RBEGamer/DBClock/documentation/images/2023-02-08 12.05.27.jpg

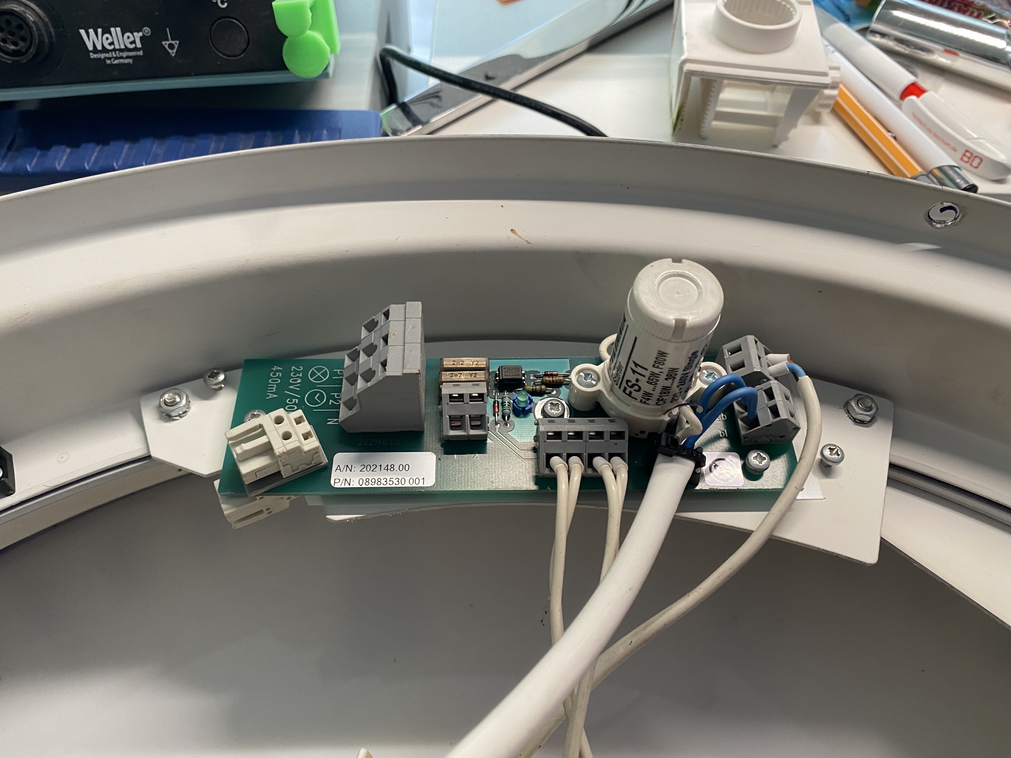
documentation/images/2023-02-08 12.05.27.jpg
