RBEGamer/DBClock/documentation/images/2023-02-08 12.11.48.jpg

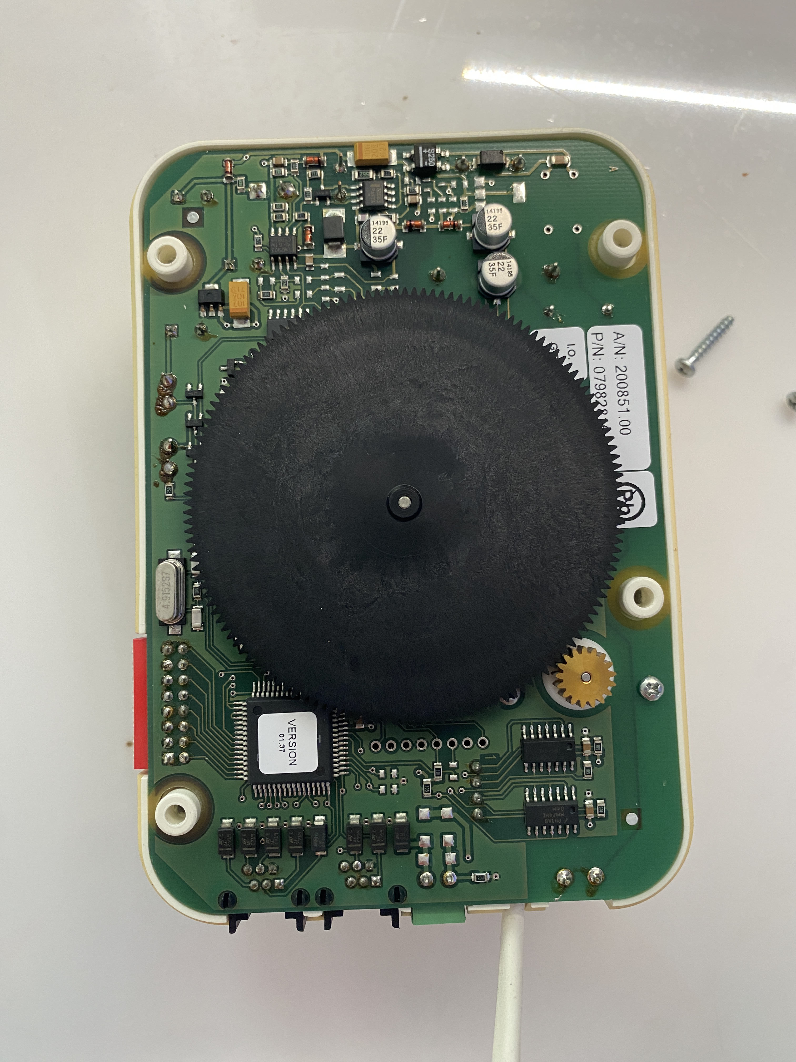
documentation/images/2023-02-08 12.11.48.jpg
