RBEGamer/DBClock/documentation/images/2023-02-12 22.21.10.jpg

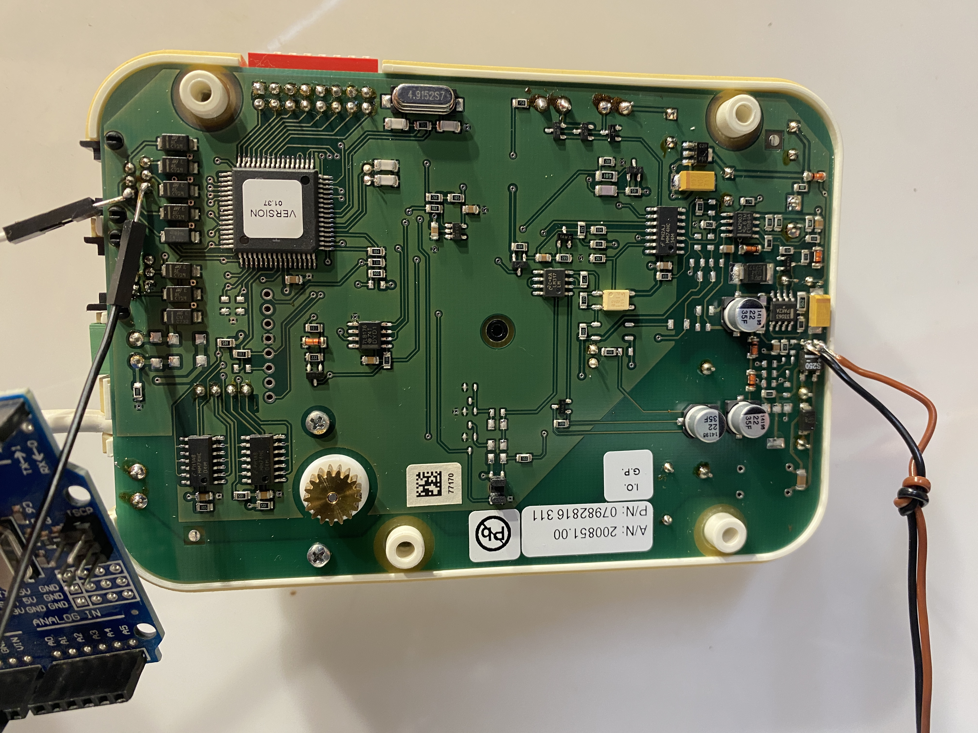
documentation/images/2023-02-12 22.21.10.jpg
