RBEGamer/DBClock/documentation/images/2023-02-13 15.05.28.jpg

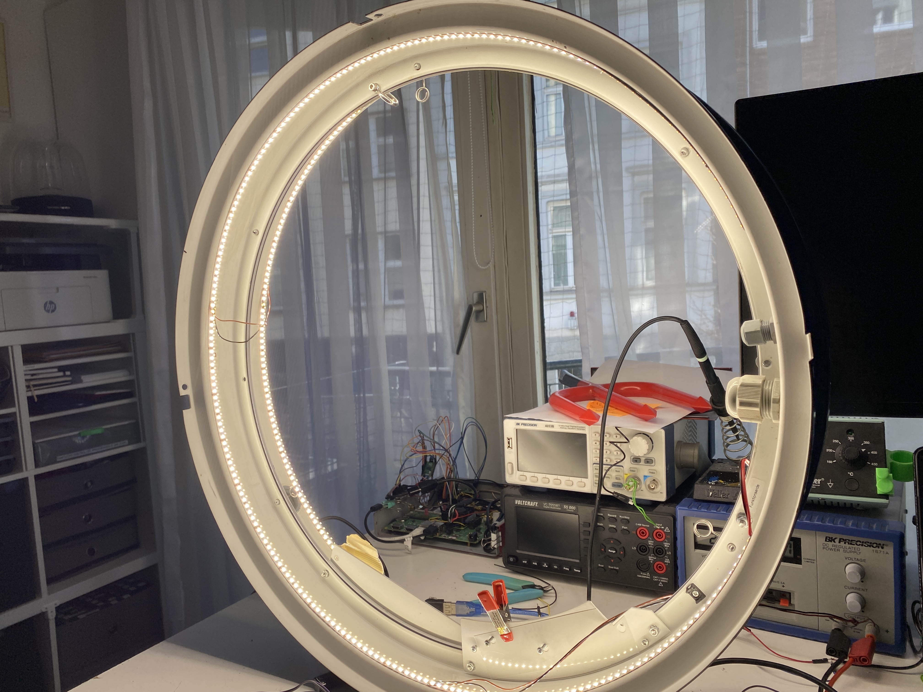
documentation/images/2023-02-13 15.05.28.jpg
