RBEGamer/DBClock/documentation/images/2023-02-14 12.46.16.jpg

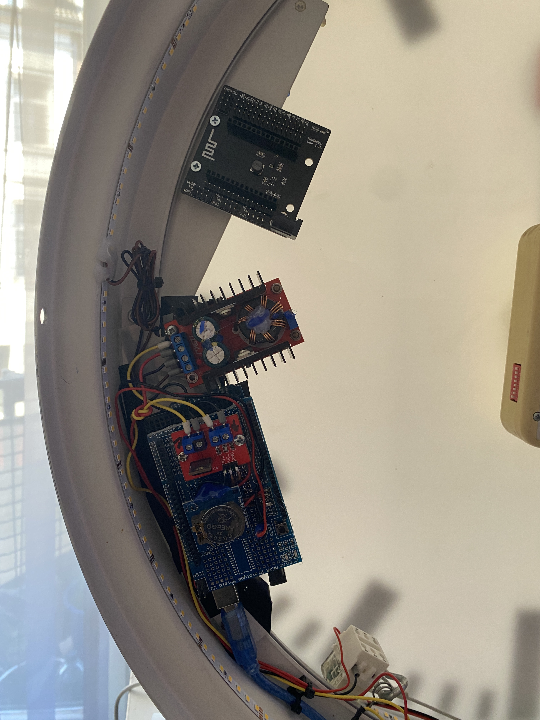
documentation/images/2023-02-14 12.46.16.jpg
