RBEGamer/DBClock/documentation/images/2023-02-14 21.41.29.jpg

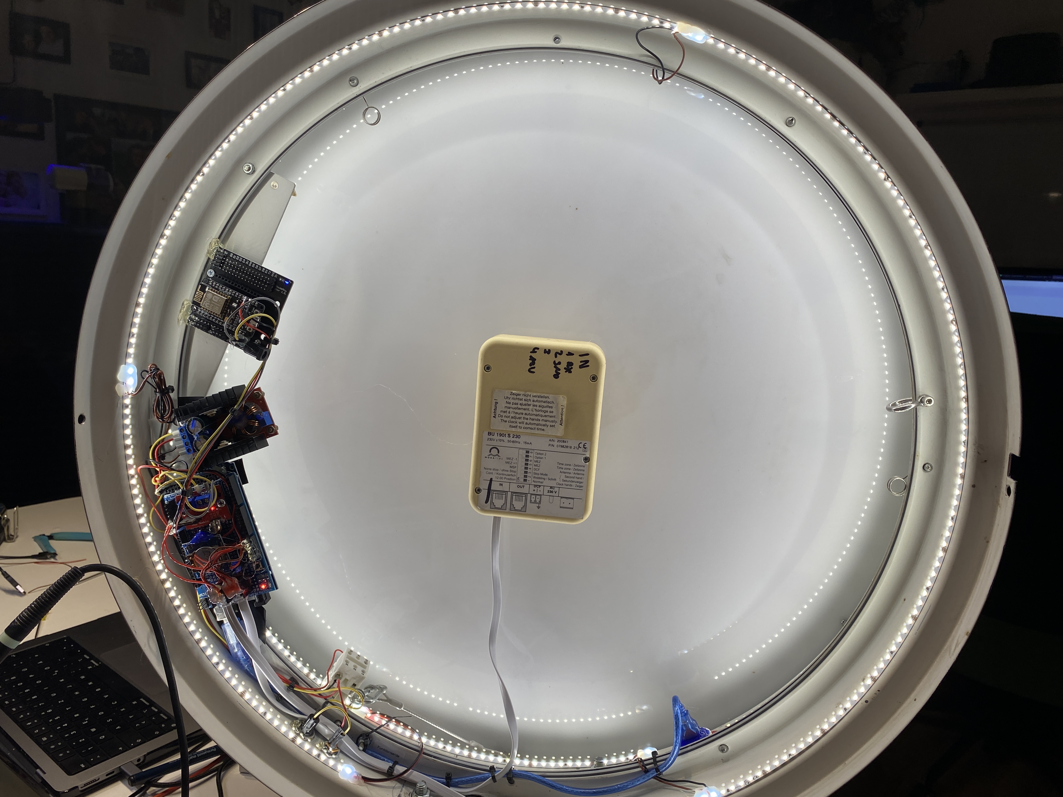
documentation/images/2023-02-14 21.41.29.jpg
