RBEGamer/DBClock/documentation/images/2023-02-12 22.24.27.jpg

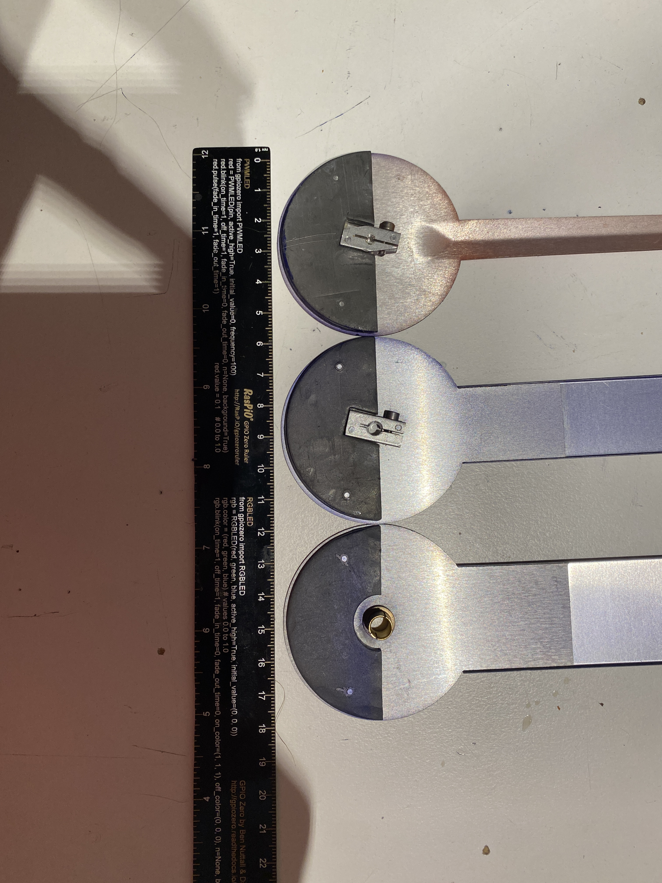
documentation/images/2023-02-12 22.24.27.jpg
